Jana-Marie/analog-toolkit/pd-dev/Core/Src/main.c

#include "main.h"
#include "cmsis_os.h"
#include "usbpd.h"

ADC_HandleTypeDef hadc1;

osThreadId defaultTaskHandle;

void SystemClock_Config(void);
static void MX_GPIO_Init(void);
static void MX_DMA_Init(void);
static void MX_UCPD1_Init(void);
static void MX_ADC1_Init(void);
static void MX_LPUART1_UART_Init(void);
void StartDefaultTask(void const * argument);

uint32_t adcVal = 0;
uint8_t pdo = 4;  // CHANGE FROM 1-5; 1: 5V; 2: 9V; 3: 15V; 4: 20V

int main(void)
{
  HAL_Init();

  SystemClock_Config();

  MX_GPIO_Init();
  MX_DMA_Init();
  MX_UCPD1_Init();
  MX_ADC1_Init();
  MX_LPUART1_UART_Init();
  
  HAL_ADC_Start(&hadc1);

  MX_USBPD_Init();

  osThreadDef(defaultTask, StartDefaultTask, osPriorityNormal, 0, 256);
  defaultTaskHandle = osThreadCreate(osThread(defaultTask), NULL);

  osKernelStart();

  while (1)
  {
  }
}

void SystemClock_Config(void)
{
  RCC_OscInitTypeDef RCC_OscInitStruct = {0};
  RCC_ClkInitTypeDef RCC_ClkInitStruct = {0};

  HAL_PWREx_ControlVoltageScaling(PWR_REGULATOR_VOLTAGE_SCALE1);

  RCC_OscInitStruct.OscillatorType = RCC_OSCILLATORTYPE_HSI;
  RCC_OscInitStruct.HSIState = RCC_HSI_ON;
  RCC_OscInitStruct.HSICalibrationValue = RCC_HSICALIBRATION_DEFAULT;
  RCC_OscInitStruct.PLL.PLLState = RCC_PLL_ON;
  RCC_OscInitStruct.PLL.PLLSource = RCC_PLLSOURCE_HSI;
  RCC_OscInitStruct.PLL.PLLM = RCC_PLLM_DIV1;
  RCC_OscInitStruct.PLL.PLLN = 8;
  RCC_OscInitStruct.PLL.PLLP = RCC_PLLP_DIV2;
  RCC_OscInitStruct.PLL.PLLQ = RCC_PLLQ_DIV2;
  RCC_OscInitStruct.PLL.PLLR = RCC_PLLR_DIV8;
  HAL_RCC_OscConfig(&RCC_OscInitStruct);

  RCC_ClkInitStruct.ClockType = RCC_CLOCKTYPE_HCLK|RCC_CLOCKTYPE_SYSCLK
                              |RCC_CLOCKTYPE_PCLK1|RCC_CLOCKTYPE_PCLK2;
  RCC_ClkInitStruct.SYSCLKSource = RCC_SYSCLKSOURCE_PLLCLK;
  RCC_ClkInitStruct.AHBCLKDivider = RCC_SYSCLK_DIV1;
  RCC_ClkInitStruct.APB1CLKDivider = RCC_HCLK_DIV1;
  RCC_ClkInitStruct.APB2CLKDivider = RCC_HCLK_DIV1;

  HAL_RCC_ClockConfig(&RCC_ClkInitStruct, FLASH_LATENCY_0);

}

static void MX_ADC1_Init(void)
{
  ADC_MultiModeTypeDef multimode = {0};
  ADC_ChannelConfTypeDef sConfig = {0};

  hadc1.Instance = ADC1;
  hadc1.Init.ClockPrescaler = ADC_CLOCK_ASYNC_DIV2;
  hadc1.Init.Resolution = ADC_RESOLUTION_12B;
  hadc1.Init.DataAlign = ADC_DATAALIGN_RIGHT;
  hadc1.Init.GainCompensation = 0;
  hadc1.Init.ScanConvMode = ADC_SCAN_DISABLE;
  hadc1.Init.EOCSelection = ADC_EOC_SEQ_CONV;
  hadc1.Init.LowPowerAutoWait = DISABLE;
  hadc1.Init.ContinuousConvMode = ENABLE;
  hadc1.Init.NbrOfConversion = 1;
  hadc1.Init.DiscontinuousConvMode = DISABLE;
  hadc1.Init.ExternalTrigConv = ADC_SOFTWARE_START;
  hadc1.Init.ExternalTrigConvEdge = ADC_EXTERNALTRIGCONVEDGE_NONE;
  hadc1.Init.DMAContinuousRequests = DISABLE;
  hadc1.Init.Overrun = ADC_OVR_DATA_OVERWRITTEN;
  hadc1.Init.OversamplingMode = DISABLE;
  HAL_ADC_Init(&hadc1);

  multimode.Mode = ADC_MODE_INDEPENDENT;
  HAL_ADCEx_MultiModeConfigChannel(&hadc1, &multimode);

  sConfig.Channel = ADC_CHANNEL_1;
  sConfig.Rank = ADC_REGULAR_RANK_1;
  sConfig.SamplingTime = ADC_SAMPLETIME_640CYCLES_5;
  sConfig.SingleDiff = ADC_SINGLE_ENDED;
  sConfig.OffsetNumber = ADC_OFFSET_NONE;
  sConfig.Offset = 0;
  HAL_ADC_ConfigChannel(&hadc1, &sConfig);

  HAL_ADCEx_Calibration_Start(&hadc1, sConfig.SingleDiff);
}

static void MX_LPUART1_UART_Init(void)
{
  LL_LPUART_InitTypeDef LPUART_InitStruct = {0};

  LL_GPIO_InitTypeDef GPIO_InitStruct = {0};
  RCC_PeriphCLKInitTypeDef PeriphClkInit = {0};

  PeriphClkInit.PeriphClockSelection = RCC_PERIPHCLK_LPUART1;
  PeriphClkInit.Lpuart1ClockSelection = RCC_LPUART1CLKSOURCE_PCLK1;
  HAL_RCCEx_PeriphCLKConfig(&PeriphClkInit);

  LL_APB1_GRP2_EnableClock(LL_APB1_GRP2_PERIPH_LPUART1);
  LL_AHB2_GRP1_EnableClock(LL_AHB2_GRP1_PERIPH_GPIOA);

  GPIO_InitStruct.Pin = LL_GPIO_PIN_2;
  GPIO_InitStruct.Mode = LL_GPIO_MODE_ALTERNATE;
  GPIO_InitStruct.Speed = LL_GPIO_SPEED_FREQ_MEDIUM;
  GPIO_InitStruct.OutputType = LL_GPIO_OUTPUT_PUSHPULL;
  GPIO_InitStruct.Pull = LL_GPIO_PULL_NO;
  GPIO_InitStruct.Alternate = LL_GPIO_AF_12;
  LL_GPIO_Init(GPIOA, &GPIO_InitStruct);

  GPIO_InitStruct.Pin = LL_GPIO_PIN_3;
  GPIO_InitStruct.Mode = LL_GPIO_MODE_ALTERNATE;
  GPIO_InitStruct.Speed = LL_GPIO_SPEED_FREQ_MEDIUM;
  GPIO_InitStruct.OutputType = LL_GPIO_OUTPUT_PUSHPULL;
  GPIO_InitStruct.Pull = LL_GPIO_PULL_NO;
  GPIO_InitStruct.Alternate = LL_GPIO_AF_12;
  LL_GPIO_Init(GPIOA, &GPIO_InitStruct);

  LL_DMA_SetPeriphRequest(DMA1, LL_DMA_CHANNEL_3, LL_DMAMUX_REQ_LPUART1_TX);

  LL_DMA_SetDataTransferDirection(DMA1, LL_DMA_CHANNEL_3, LL_DMA_DIRECTION_MEMORY_TO_PERIPH);

  LL_DMA_SetChannelPriorityLevel(DMA1, LL_DMA_CHANNEL_3, LL_DMA_PRIORITY_HIGH);

  LL_DMA_SetMode(DMA1, LL_DMA_CHANNEL_3, LL_DMA_MODE_NORMAL);

  LL_DMA_SetPeriphIncMode(DMA1, LL_DMA_CHANNEL_3, LL_DMA_PERIPH_NOINCREMENT);

  LL_DMA_SetMemoryIncMode(DMA1, LL_DMA_CHANNEL_3, LL_DMA_MEMORY_INCREMENT);

  LL_DMA_SetPeriphSize(DMA1, LL_DMA_CHANNEL_3, LL_DMA_PDATAALIGN_BYTE);

  LL_DMA_SetMemorySize(DMA1, LL_DMA_CHANNEL_3, LL_DMA_MDATAALIGN_BYTE);

  NVIC_SetPriority(LPUART1_IRQn, NVIC_EncodePriority(NVIC_GetPriorityGrouping(),3, 0));
  NVIC_EnableIRQ(LPUART1_IRQn);

  LPUART_InitStruct.PrescalerValue = LL_LPUART_PRESCALER_DIV1;
  LPUART_InitStruct.BaudRate = 115200;
  LPUART_InitStruct.DataWidth = LL_LPUART_DATAWIDTH_8B;
  LPUART_InitStruct.StopBits = LL_LPUART_STOPBITS_1;
  LPUART_InitStruct.Parity = LL_LPUART_PARITY_NONE;
  LPUART_InitStruct.TransferDirection = LL_LPUART_DIRECTION_TX_RX;
  LPUART_InitStruct.HardwareFlowControl = LL_LPUART_HWCONTROL_NONE;
  LL_LPUART_Init(LPUART1, &LPUART_InitStruct);
  LL_LPUART_SetTXFIFOThreshold(LPUART1, LL_LPUART_FIFOTHRESHOLD_1_8);
  LL_LPUART_SetRXFIFOThreshold(LPUART1, LL_LPUART_FIFOTHRESHOLD_1_8);
  LL_LPUART_DisableFIFO(LPUART1);

  LL_LPUART_Enable(LPUART1);

  while((!(LL_LPUART_IsActiveFlag_TEACK(LPUART1))) || (!(LL_LPUART_IsActiveFlag_REACK(LPUART1))))
  {
  }
}

static void MX_UCPD1_Init(void)
{
  LL_GPIO_InitTypeDef GPIO_InitStruct = {0};

  LL_APB1_GRP2_EnableClock(LL_APB1_GRP2_PERIPH_UCPD1);

  LL_AHB2_GRP1_EnableClock(LL_AHB2_GRP1_PERIPH_GPIOB);

  GPIO_InitStruct.Pin = LL_GPIO_PIN_4;
  GPIO_InitStruct.Mode = LL_GPIO_MODE_ANALOG;
  GPIO_InitStruct.Pull = LL_GPIO_PULL_NO;
  LL_GPIO_Init(GPIOB, &GPIO_InitStruct);

  GPIO_InitStruct.Pin = LL_GPIO_PIN_6;
  GPIO_InitStruct.Mode = LL_GPIO_MODE_ANALOG;
  GPIO_InitStruct.Pull = LL_GPIO_PULL_NO;
  LL_GPIO_Init(GPIOB, &GPIO_InitStruct);

  LL_DMA_SetPeriphRequest(DMA1, LL_DMA_CHANNEL_1, LL_DMAMUX_REQ_UCPD1_RX);

  LL_DMA_SetDataTransferDirection(DMA1, LL_DMA_CHANNEL_1, LL_DMA_DIRECTION_PERIPH_TO_MEMORY);

  LL_DMA_SetChannelPriorityLevel(DMA1, LL_DMA_CHANNEL_1, LL_DMA_PRIORITY_LOW);

  LL_DMA_SetMode(DMA1, LL_DMA_CHANNEL_1, LL_DMA_MODE_NORMAL);

  LL_DMA_SetPeriphIncMode(DMA1, LL_DMA_CHANNEL_1, LL_DMA_PERIPH_NOINCREMENT);

  LL_DMA_SetMemoryIncMode(DMA1, LL_DMA_CHANNEL_1, LL_DMA_MEMORY_INCREMENT);

  LL_DMA_SetPeriphSize(DMA1, LL_DMA_CHANNEL_1, LL_DMA_PDATAALIGN_BYTE);

  LL_DMA_SetMemorySize(DMA1, LL_DMA_CHANNEL_1, LL_DMA_MDATAALIGN_BYTE);

  LL_DMA_SetPeriphRequest(DMA1, LL_DMA_CHANNEL_2, LL_DMAMUX_REQ_UCPD1_TX);

  LL_DMA_SetDataTransferDirection(DMA1, LL_DMA_CHANNEL_2, LL_DMA_DIRECTION_MEMORY_TO_PERIPH);

  LL_DMA_SetChannelPriorityLevel(DMA1, LL_DMA_CHANNEL_2, LL_DMA_PRIORITY_LOW);

  LL_DMA_SetMode(DMA1, LL_DMA_CHANNEL_2, LL_DMA_MODE_NORMAL);

  LL_DMA_SetPeriphIncMode(DMA1, LL_DMA_CHANNEL_2, LL_DMA_PERIPH_NOINCREMENT);

  LL_DMA_SetMemoryIncMode(DMA1, LL_DMA_CHANNEL_2, LL_DMA_MEMORY_INCREMENT);

  LL_DMA_SetPeriphSize(DMA1, LL_DMA_CHANNEL_2, LL_DMA_PDATAALIGN_BYTE);

  LL_DMA_SetMemorySize(DMA1, LL_DMA_CHANNEL_2, LL_DMA_MDATAALIGN_BYTE);

  NVIC_SetPriority(UCPD1_IRQn, NVIC_EncodePriority(NVIC_GetPriorityGrouping(),3, 0));
  NVIC_EnableIRQ(UCPD1_IRQn);
}

static void MX_DMA_Init(void)
{

  __HAL_RCC_DMAMUX1_CLK_ENABLE();
  __HAL_RCC_DMA1_CLK_ENABLE();

  NVIC_SetPriority(DMA1_Channel1_IRQn, NVIC_EncodePriority(NVIC_GetPriorityGrouping(),3, 0));
  NVIC_EnableIRQ(DMA1_Channel1_IRQn);
  NVIC_SetPriority(DMA1_Channel2_IRQn, NVIC_EncodePriority(NVIC_GetPriorityGrouping(),3, 0));
  NVIC_EnableIRQ(DMA1_Channel2_IRQn);
  NVIC_SetPriority(DMA1_Channel3_IRQn, NVIC_EncodePriority(NVIC_GetPriorityGrouping(),3, 0));
  NVIC_EnableIRQ(DMA1_Channel3_IRQn);

}

static void MX_GPIO_Init(void)
{
  __HAL_RCC_GPIOA_CLK_ENABLE();
  __HAL_RCC_GPIOB_CLK_ENABLE();
}

void StartDefaultTask(void const * argument)
{
  for(;;)
  {
    osDelay(10);
    adcVal = HAL_ADC_GetValue(&hadc1);
  }
}

void Error_Handler(void)
{
  __disable_irq();
  while (1)
  {
  }
}

#ifdef  USE_FULL_ASSERT

void assert_failed(uint8_t *file, uint32_t line)
{

}
#endif
