Jana-Marie/analog-toolkit/DAC/Core/Inc/brrrrp.h

#ifndef __BRRRRP_H
#define __BRRRRP_H

uint8_t buzzer[25142] = {128, 128, 128, 128, 128, 127, 128, 127, 128, 127, 128, 128, 127, 128, 127, 128, 128, 127, 128, 127, 128, 128, 127, 128, 127, 128, 128, 127, 128, 127, 128, 127, 128, 127, 128, 127, 128, 127, 128, 127, 128, 128, 128, 128, 127, 128, 128, 128, 128, 127, 128, 127, 128, 127, 128, 127, 128, 127, 128, 127, 128, 127, 128, 128, 128, 128, 127, 128, 127, 128, 127, 128, 127, 128, 127, 128, 128, 128, 128, 128, 128, 128, 128, 128, 128, 128, 128, 128, 128, 128, 128, 128, 127, 128, 127, 128, 127, 128, 128, 127, 128, 127, 128, 128, 128, 128, 127, 128, 127, 128, 127, 128, 128, 128, 128, 128, 128, 128, 128, 127, 128, 127, 128, 127, 128, 128, 127, 128, 128, 128, 127, 128, 127, 128, 128, 127, 128, 127, 127, 128, 127, 128, 127, 128, 128, 128, 127, 128, 127, 128, 128, 127, 128, 128, 127, 128, 127, 128, 127, 128, 127, 128, 127, 128, 127, 128, 127, 128, 128, 127, 128, 127, 128, 128, 127, 128, 127, 128, 127, 128, 127, 128, 128, 127, 128, 127, 128, 128, 127, 128, 128, 127, 128, 127, 128, 127, 128, 127, 128, 128, 127, 128, 127, 128, 127, 128, 127, 128, 127, 128, 127, 128, 128, 127, 128, 127, 127, 128, 127, 128, 127, 128, 127, 128, 127, 128, 128, 127, 128, 127, 128, 128, 128, 127, 128, 127, 128, 127, 128, 128, 127, 128, 127, 128, 127, 128, 127, 128, 127, 128, 128, 127, 128, 128, 127, 128, 128, 127, 128, 128, 127, 128, 127, 128, 127, 128, 127, 128, 127, 128, 128, 127, 128, 127, 128, 127, 128, 127, 128, 128, 128, 128, 128, 127, 128, 128, 128, 127, 128, 127, 128, 128, 127, 128, 127, 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
